jamesjnadeau/refGearDownCounter/down-indicator-string/tests/scad/logo_only.scad

use <../../lib/body.scad>
use <../../lib/logo.scad>

bodyLen = 40.0;
bodyWid = 30.0;
bodyT   =  6.7;

logoWidth = 26.0;
logoDepth =  0.5;
logoX     = -8.75;
logoY     =   0.0;
$fn = 96;

difference() {
    body_blank(bodyLen, bodyWid, bodyT);
    logo_cutter(bodyT, logoWidth, logoDepth, logoX, logoY);
}
